H3ndrik-Jan/Differential_probe/Measurements/Pictures/IMG1.JPG

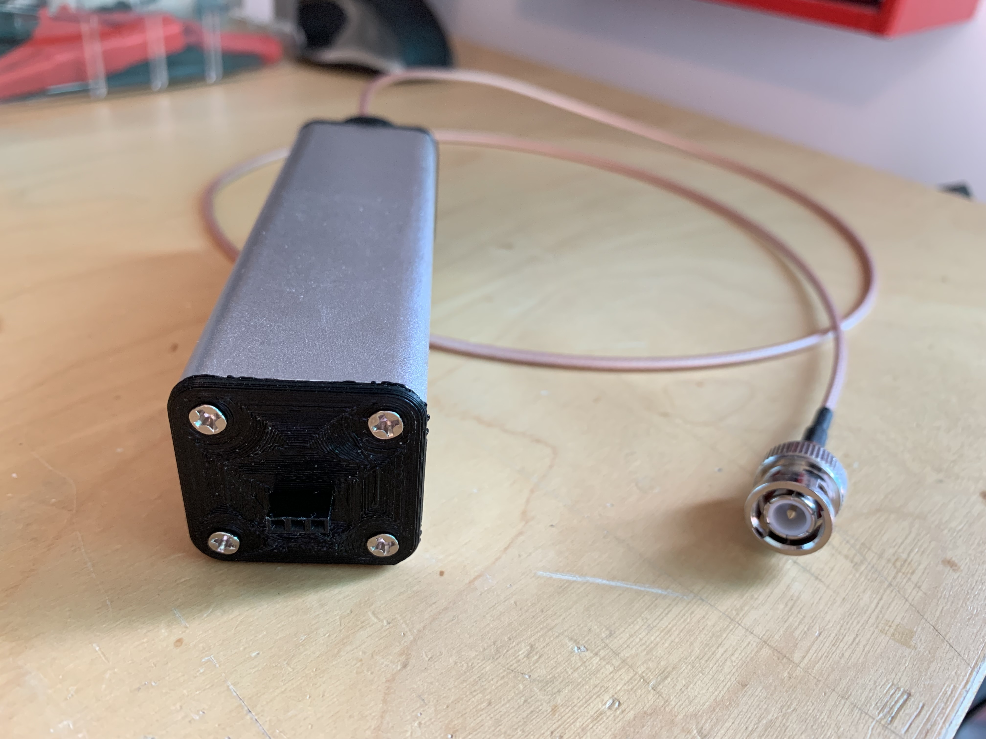
Measurements/Pictures/IMG1.JPG
