H3ndrik-Jan/Differential_probe/Sim/battery_indicator.asc

C1: cap; 10µ
D1: LED; NSPW500BS
Q2: npn; 2N3904
R1: res; 47K
R2: res; 33K
R3: res; 27K
R4: res; 47K
R5: res; 47K
R6: res; 47K
R7: res; 1K
R8: res; 47K
R9: res; 10K
U1: LTC1841
U2: LTC1841
V1: voltage; 3
V2: voltage; 5.45
Named nets: V+, 0
.tran 20 startup uic
