H3ndrik-Jan/Differential_probe/Sim/Batteryswitch.asc

BAT: voltage; 3.7; Rser=1
C1: cap; 10µ
D2: diode; 1N4148
D3: diode; 1N4148
D4: diode; 1N4148
M1: pmos; BSS84
M2: pmos; BSS84
Q1: npn; 2N3904
Q2: pnp; 2N3906
R1: res; 100K
R2: res; 200K
R3: res; 20K
R4: res; 20K
R5: res; 100K
V1: voltage; 5; Rser=1
VUSB: voltage; 5
Named nets: 0, VBAT, bus
.tran 1
The circuit acts as power switch and reduces leakage currents when the load is turned off.
