H3ndrik-Jan/Differential_probe/Sim/Diffprobe.asc

C1: cap; 0p
C2: cap; 0p
C3: cap; 26p
C4: cap; 26p
C5: cap; 3p
C7: cap; 3p
C15: cap; 1p
C16: cap; 1p
R1: res; 330
R2: res; 20K
R3: res; 330
R4: res; 2Meg
R5: res; 2Meg
R6: res; 402K
R7: res; 402K
R10: res; 1K
R11: res; 330
R12: res; 330
R13: res; 330
R14: res; 330
R15: res; 1Meg
R17: res; 1K
R18: res; 2Meg
R19: res; 2Meg
R20: res; 42.2K
R21: res; 42.2K
R31: res; 0
R32: res; 0
U1: ADA4817
U4: ADA4817
U5: LTC6228
V1: voltage; SINE(2 5 100k); AC 1
V2: voltage; 0
V3: voltage; 5
V4: voltage; 5
V5: voltage; SINE(0 1 500k)
V6: voltage; SINE(0 1 200K)
Named nets: IN+, IN-, 0, Vbias, V+, V-
.tran 0.1
.lib ada4817.cir
